ji1udd/HL2-PA30/Doc/PowerMeter/RD15_RD16_comparison_on_PA30.jpg

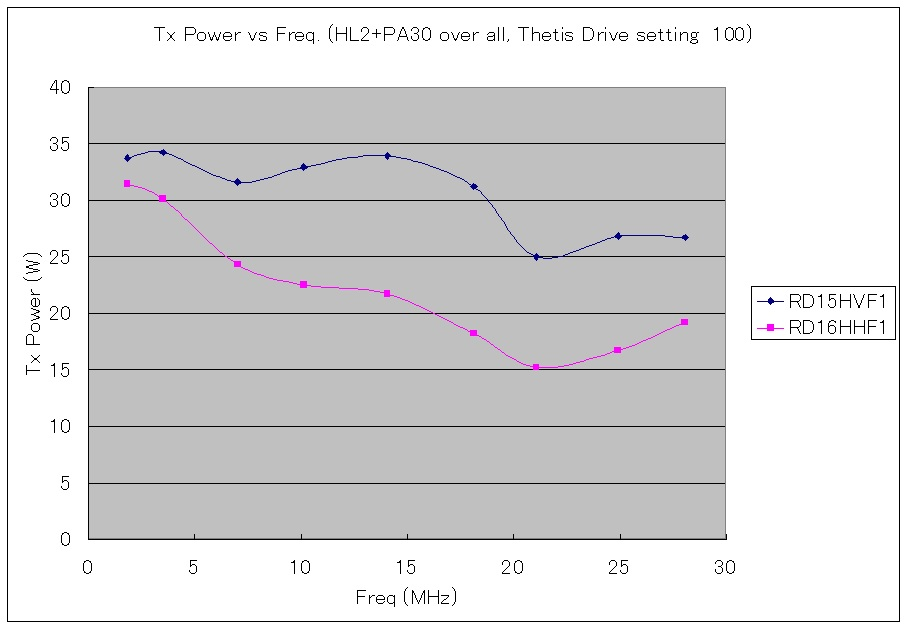
Doc/PowerMeter/RD15_RD16_comparison_on_PA30.jpg
