ji1udd/HL2-PA30/Doc/PureSignal/IMD_40M_30W_PS-OFF.jpg

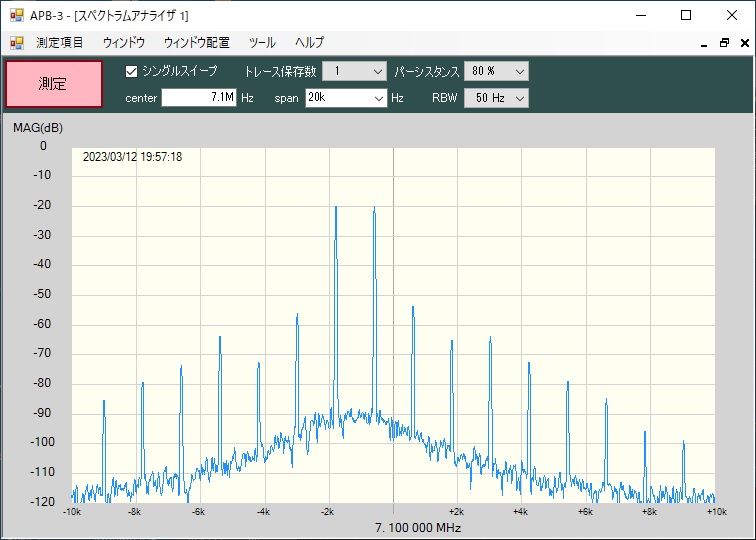
Doc/PureSignal/IMD_40M_30W_PS-OFF.jpg
