ji1udd/HL2-PA30/Doc/Spur/Spur_20M_30W.jpg

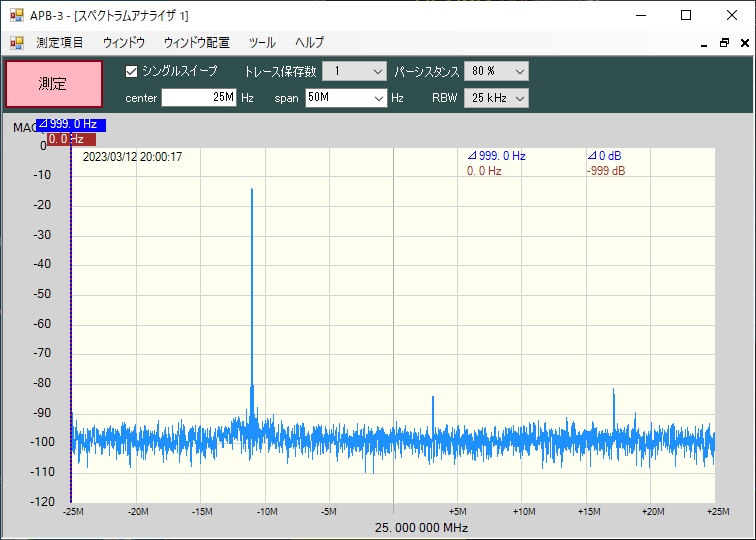
Doc/Spur/Spur_20M_30W.jpg
