ji1udd/HL2-PA30/Doc/Assemble/CN4_1.jpg

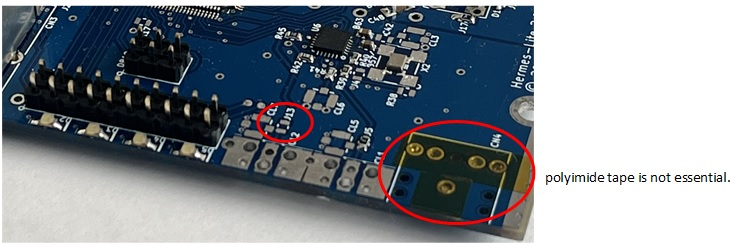
Doc/Assemble/CN4_1.jpg
