ji1udd/HL2-PA30/Doc/Assemble/CN4_2.jpg

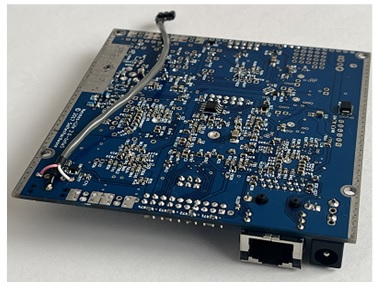
Doc/Assemble/CN4_2.jpg
