ji1udd/HL2-PA30/Doc/Assemble/fan.jpg

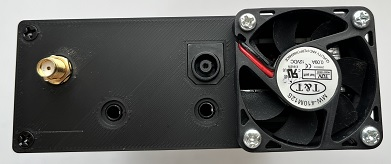
Doc/Assemble/fan.jpg
