ji1udd/HL2-PA30/Doc/Assemble/HL2_PinHeader.jpg

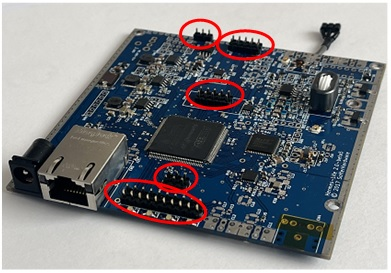
Doc/Assemble/HL2_PinHeader.jpg
