ji1udd/HL2-PA30/Doc/Assemble/LowProfilePinHeader.jpg

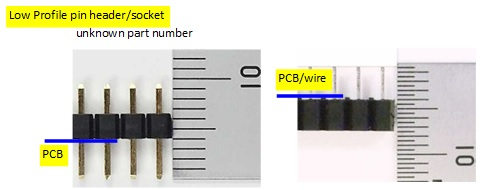
Doc/Assemble/LowProfilePinHeader.jpg
