ji1udd/HL2-PA30/Doc/Assemble/RD15Tab.jpg

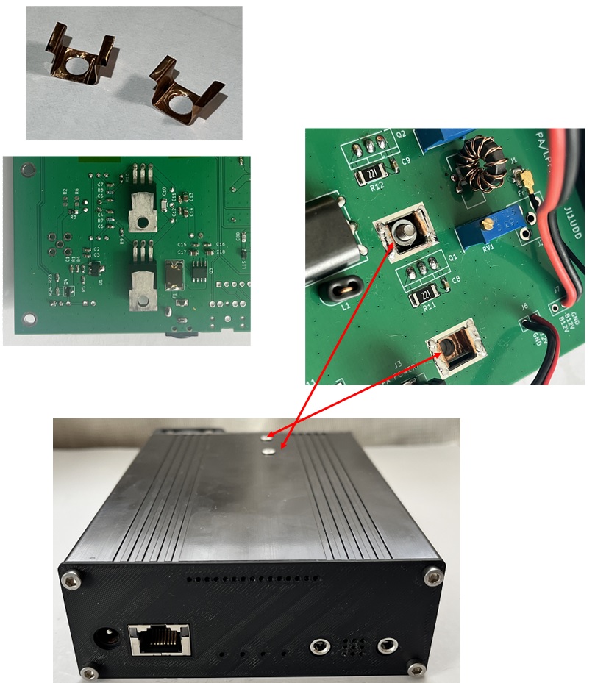
Doc/Assemble/RD15Tab.jpg
