ji1udd/HL2-PA30/Doc/Assemble/relay_shield.jpg

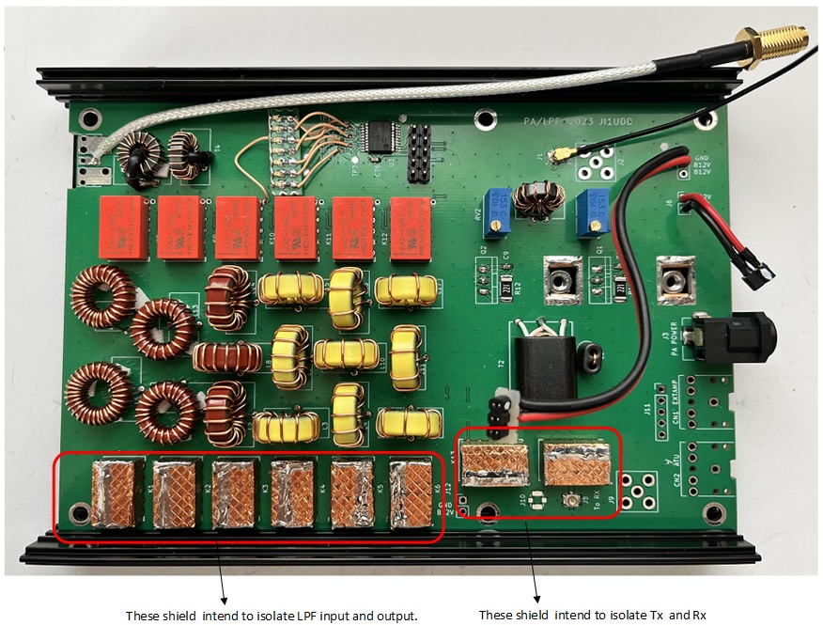
Doc/Assemble/relay_shield.jpg
