ji1udd/HL2-PA30/Doc/Assemble/stacked_boards.jpg

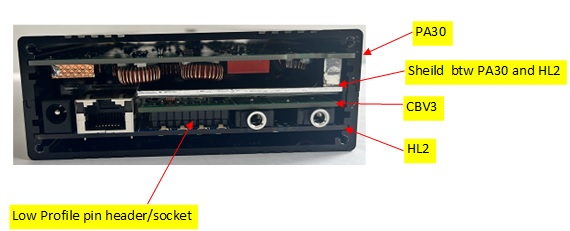
Doc/Assemble/stacked_boards.jpg
