ji1udd/HL2-PA30/Doc/Assemble/T2_4turns_1turnx2.jpg

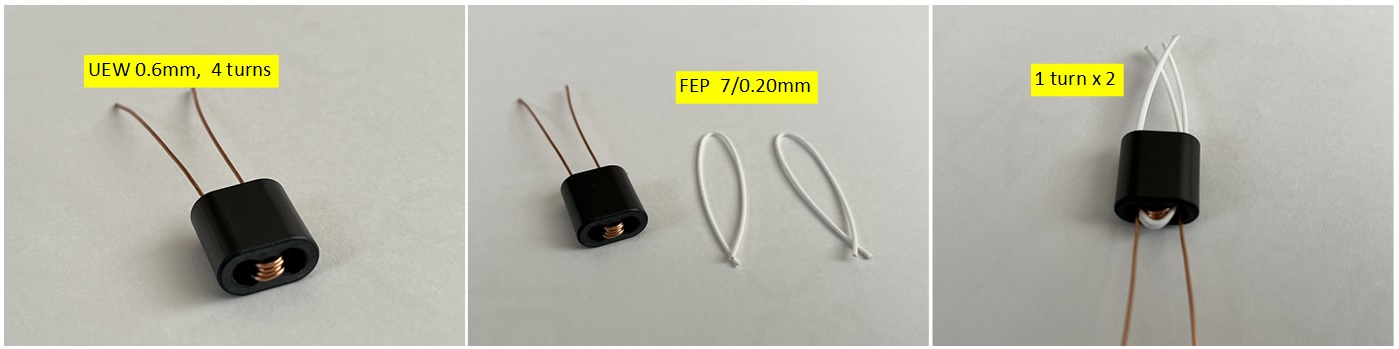
Doc/Assemble/T2_4turns_1turnx2.jpg
