ji1udd/HL2-PA30/Doc/PowerMeter/Test_FwdMeter_40M_CW.jpg

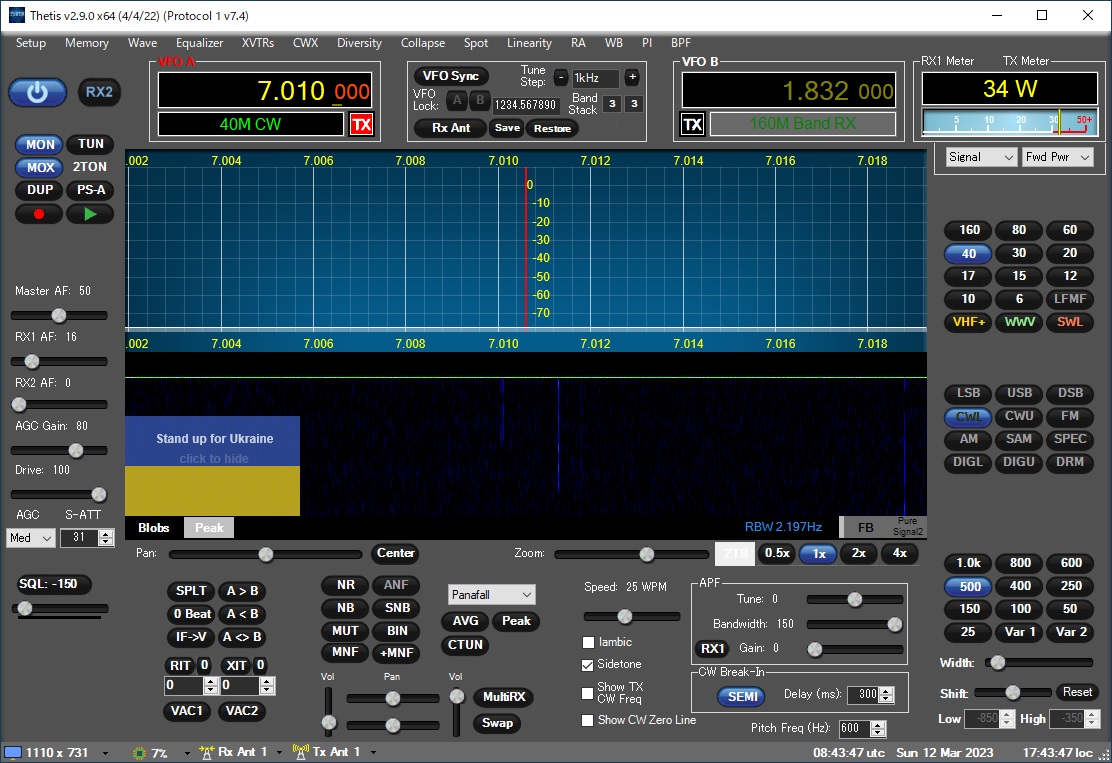
Doc/PowerMeter/Test_FwdMeter_40M_CW.jpg
